BaiTianio/VLP/Data_Receive_analyze/Analyze_Python/2020_1_13实验分析/俯仰角/解决方法3/Picture/PDPD10-20.jpg

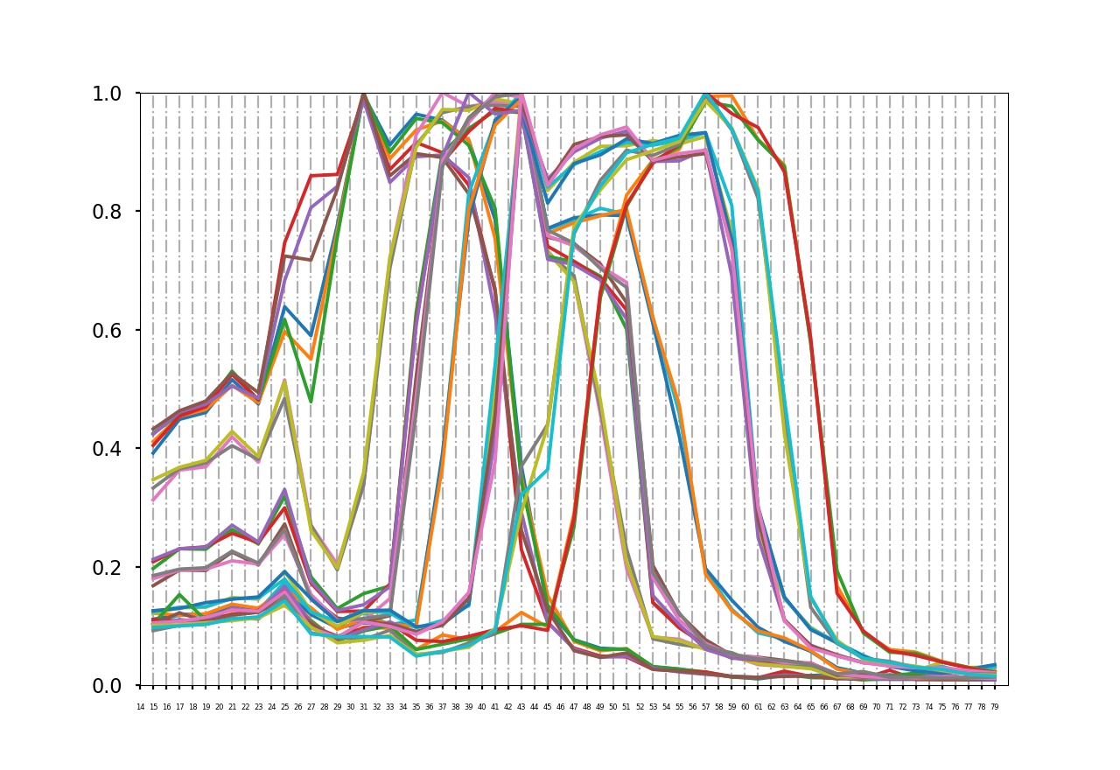
Data_Receive_analyze/Analyze_Python/2020_1_13实验分析/俯仰角/解决方法3/Picture/PDPD10-20.jpg
