BaiTianio/VLP/Data_Receive_analyze/Analyze_Matlab/picture/8PDsV2/PDarray1_39.jpg

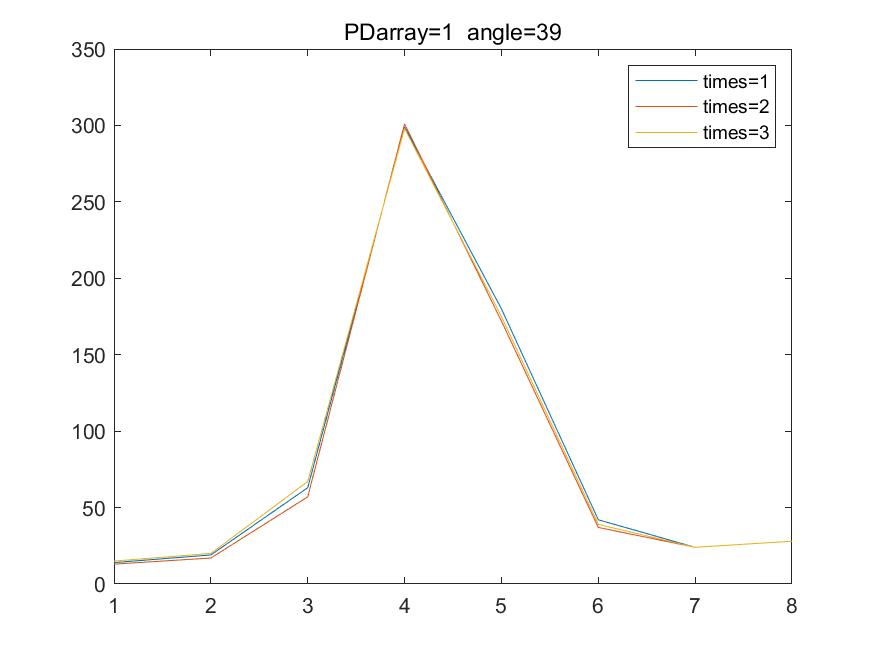
Data_Receive_analyze/Analyze_Matlab/picture/8PDsV2/PDarray1_39.jpg
