BaiTianio/VLP/Data_Receive_analyze/Analyze_Matlab/picture/8PDsV2/PDarray2_62.jpg

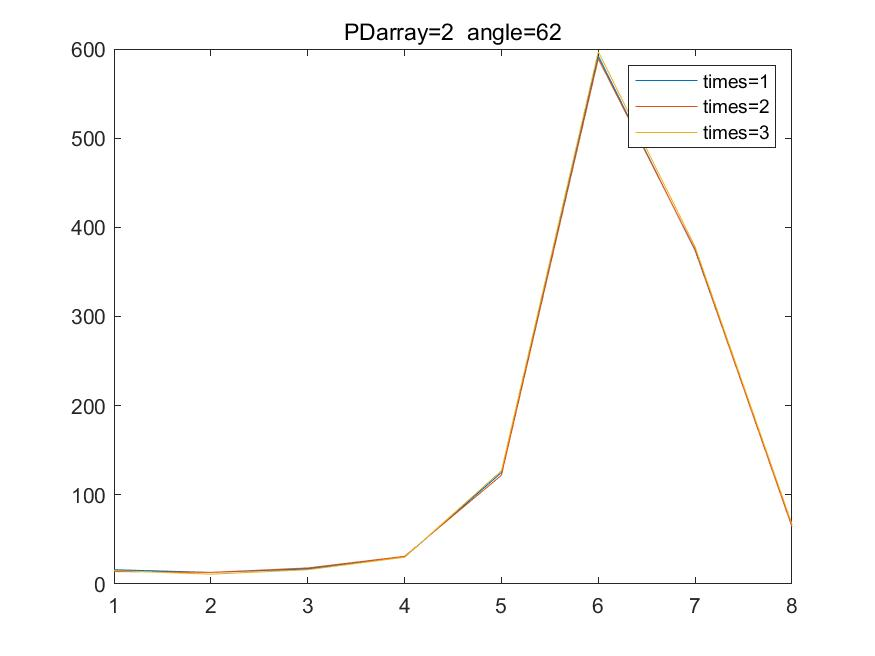
Data_Receive_analyze/Analyze_Matlab/picture/8PDsV2/PDarray2_62.jpg
