BaiTianio/VLP/Data_Receive_analyze/Analyze_Matlab/picture/8PDsV2/PDarray4_66.jpg

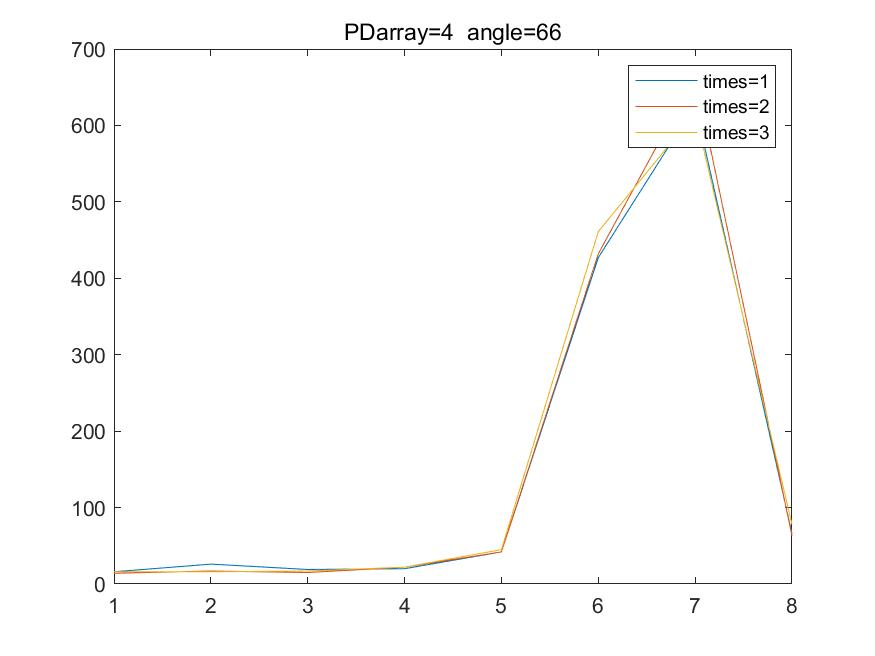
Data_Receive_analyze/Analyze_Matlab/picture/8PDsV2/PDarray4_66.jpg
