BaiTianio/VLP/Data_Receive_analyze/Analyze_Matlab/picture/32PDsV2/Angle_74.jpg

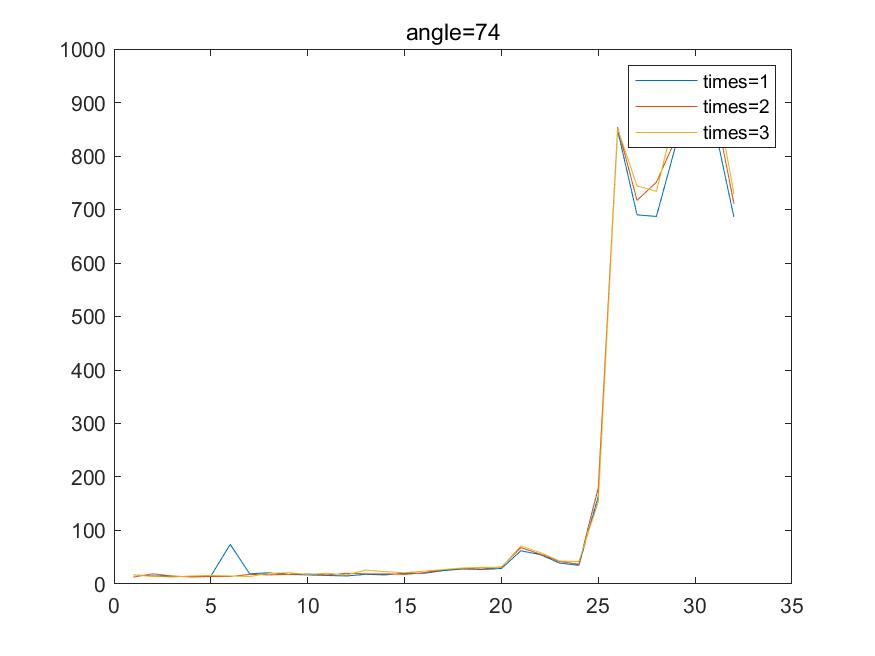
Data_Receive_analyze/Analyze_Matlab/picture/32PDsV2/Angle_74.jpg
