BaiTianio/VLP/Data_Receive_analyze/Analyze_Matlab/picture/32PDsV2/Angle_80.jpg

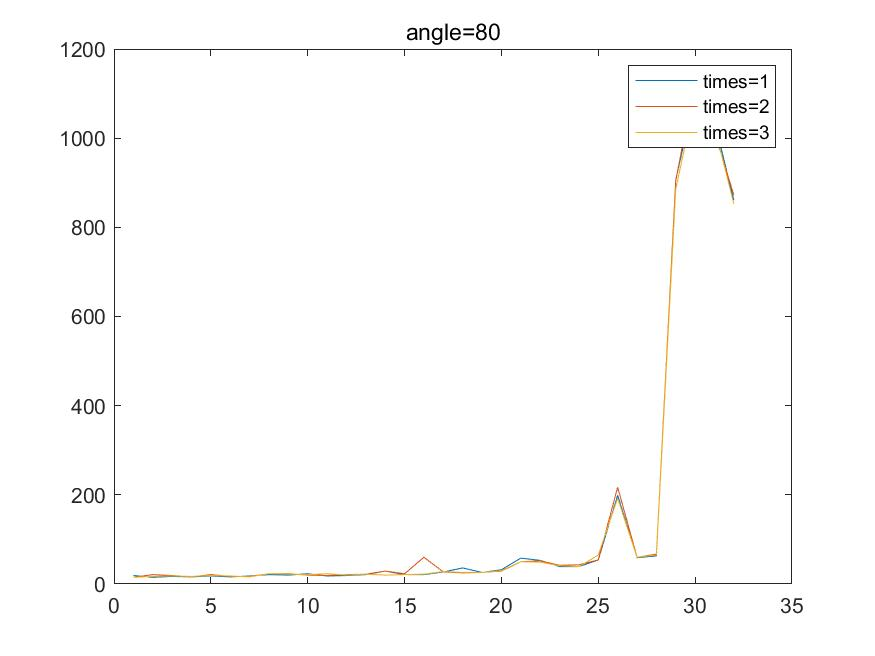
Data_Receive_analyze/Analyze_Matlab/picture/32PDsV2/Angle_80.jpg
