BaiTianio/VLP/Data_Receive_analyze/Analyze_Matlab/picture/SignlePD/PD32.jpg

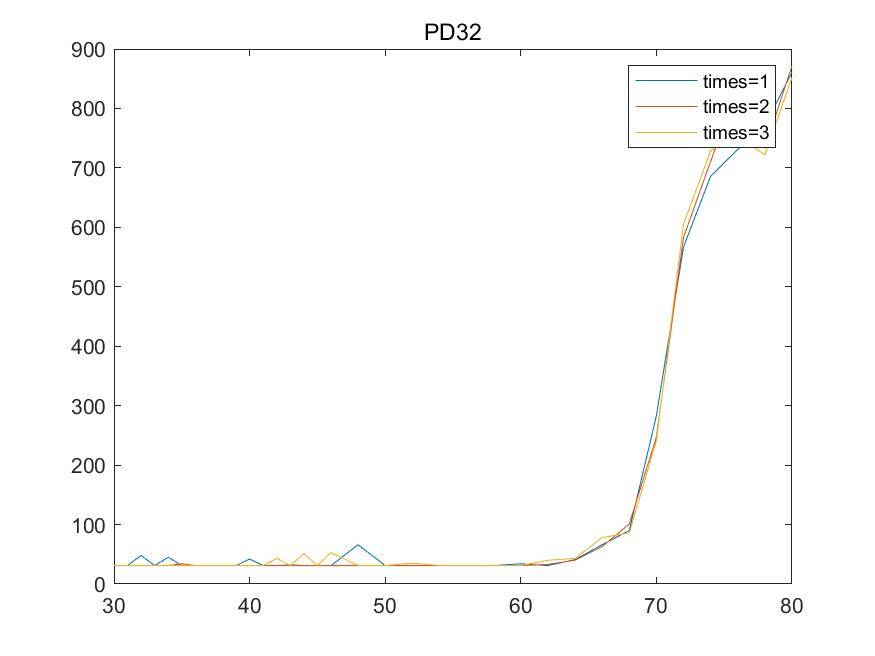
Data_Receive_analyze/Analyze_Matlab/picture/SignlePD/PD32.jpg
