BaiTianio/VLP/Data_Receive_analyze/Analyze_Python/2019_8_23实验分析/俯仰角/解决方法1/Picture/rearrange/31_1.jpg

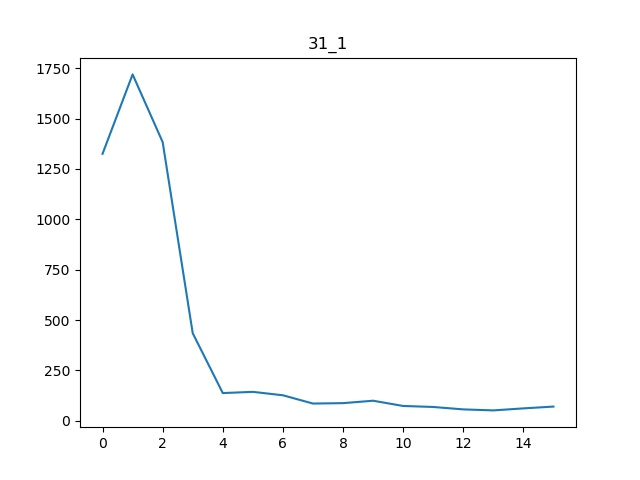
Data_Receive_analyze/Analyze_Python/2019_8_23实验分析/俯仰角/解决方法1/Picture/rearrange/31_1.jpg
