BaiTianio/VLP/Data_Receive_analyze/Analyze_Python/2019_8_23实验分析/水平角/picture/horizontalAngle_32PD/angle29_3.png

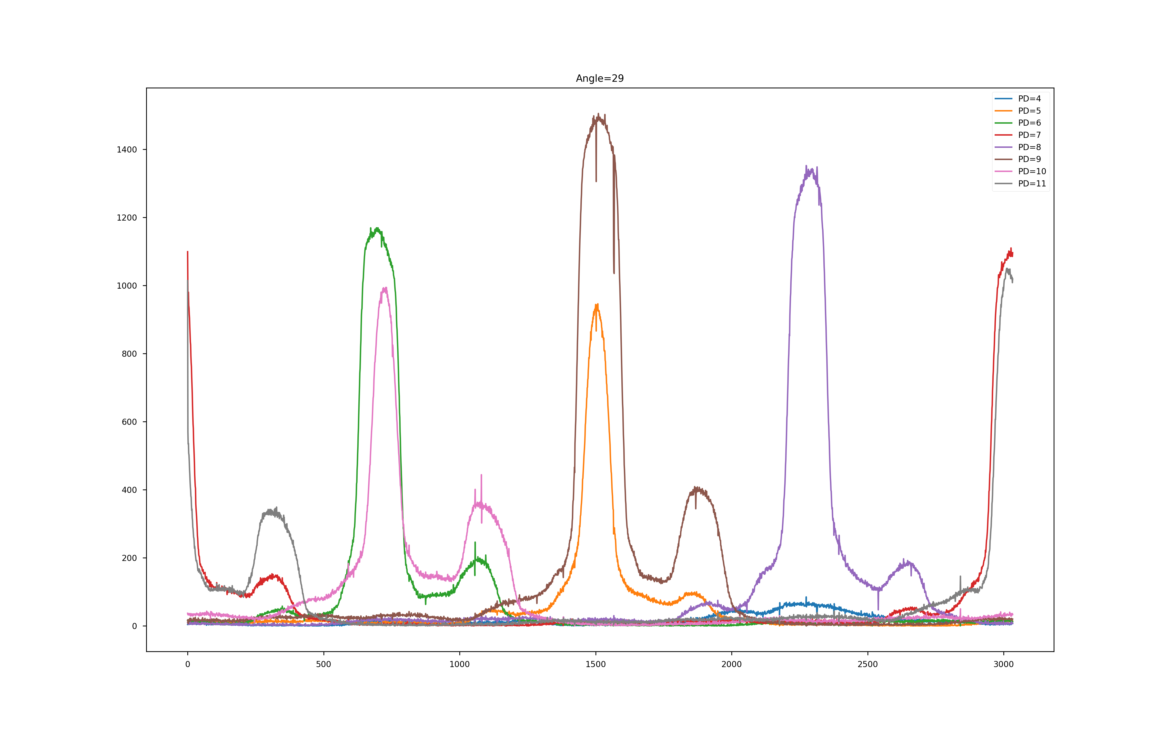
Data_Receive_analyze/Analyze_Python/2019_8_23实验分析/水平角/picture/horizontalAngle_32PD/angle29_3.png
