BaiTianio/VLP/Data_Receive_analyze/Analyze_Python/2020_1_13实验分析/俯仰角/解决方法1/Picture/singlePD/PD20.jpg

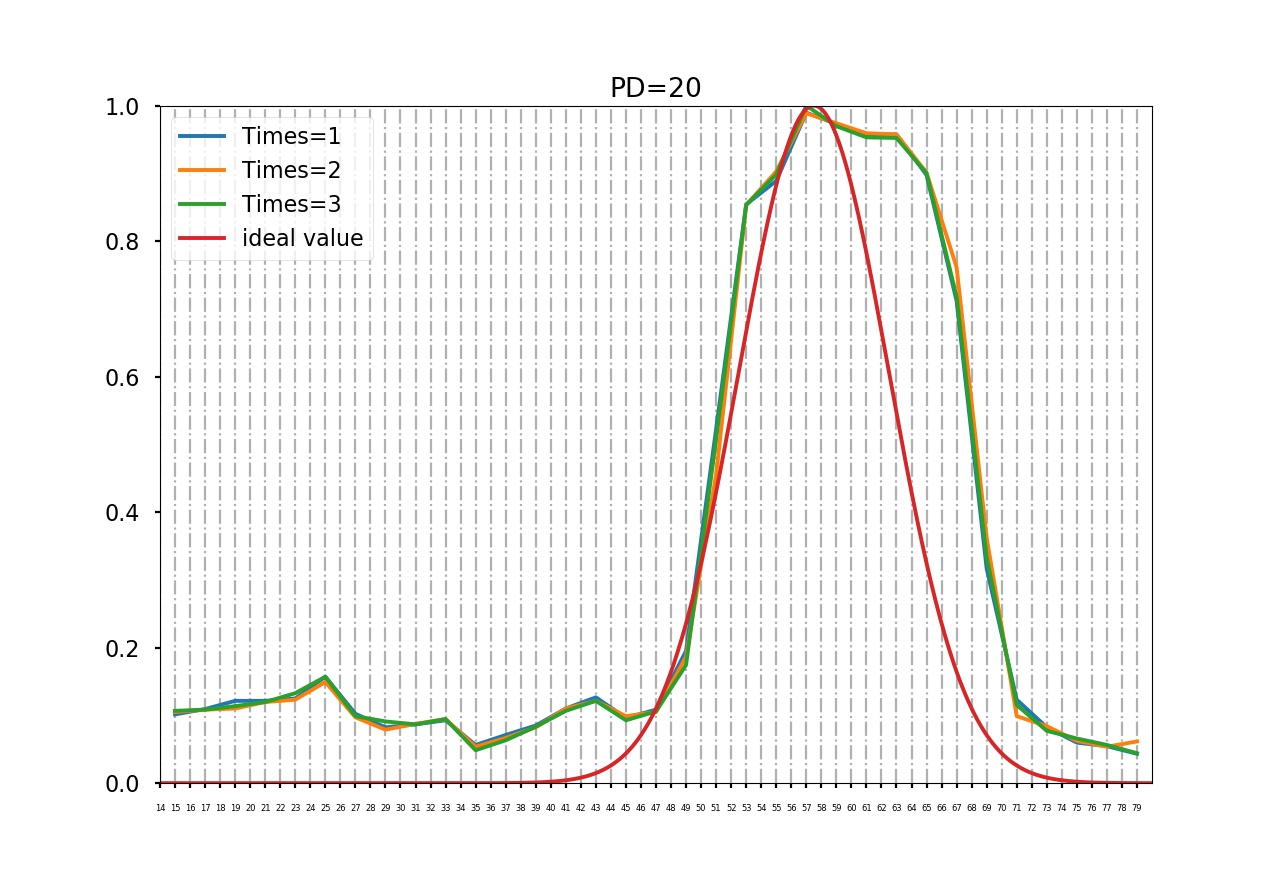
Data_Receive_analyze/Analyze_Python/2020_1_13实验分析/俯仰角/解决方法1/Picture/singlePD/PD20.jpg
