BaiTianio/VLP/Data_Receive_analyze/DataStroge/2019_8_23/Picture/siglePD_15_79/20.jpg

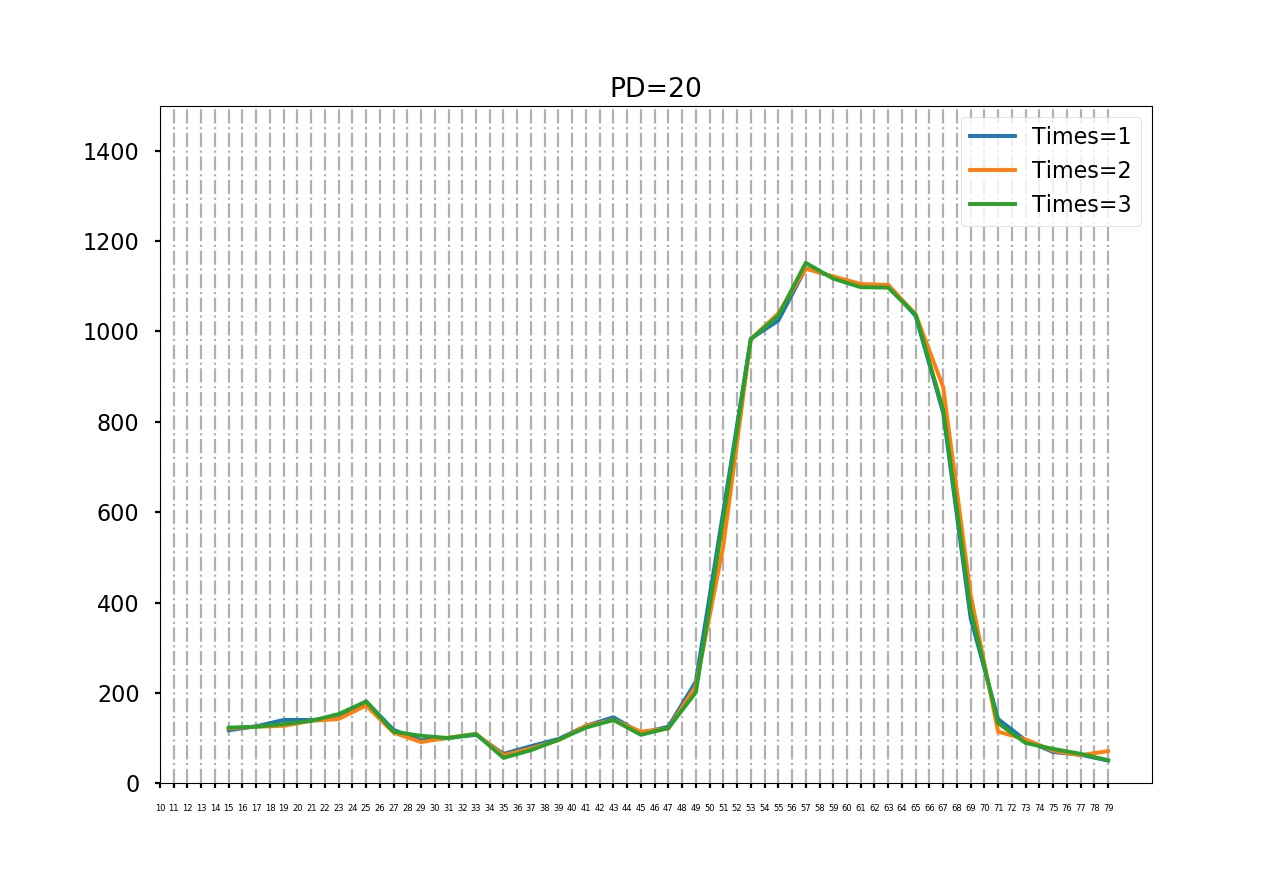
Data_Receive_analyze/DataStroge/2019_8_23/Picture/siglePD_15_79/20.jpg
