BaiTianio/VLP/Receiver/Construction_Design(SW)/转台/V3/电机.SLDPRT

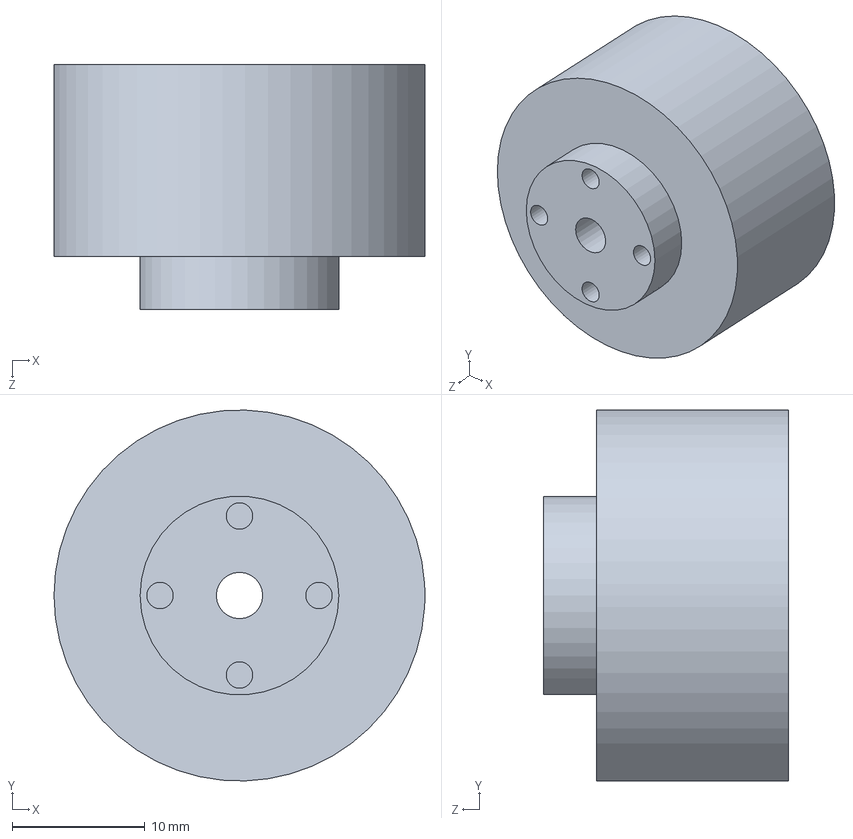
[picture p196: CAD file, 2020-01-13]
Receiver/Construction_Design(SW)/转台/V3/电机.SLDPRT
28.0 x 28.0 x 18.5 mm
