BaiTianio/VLP/Receiver/Construction_Design(SW)/转台/V3/齿轮/3号齿轮Part_a.SLDPRT

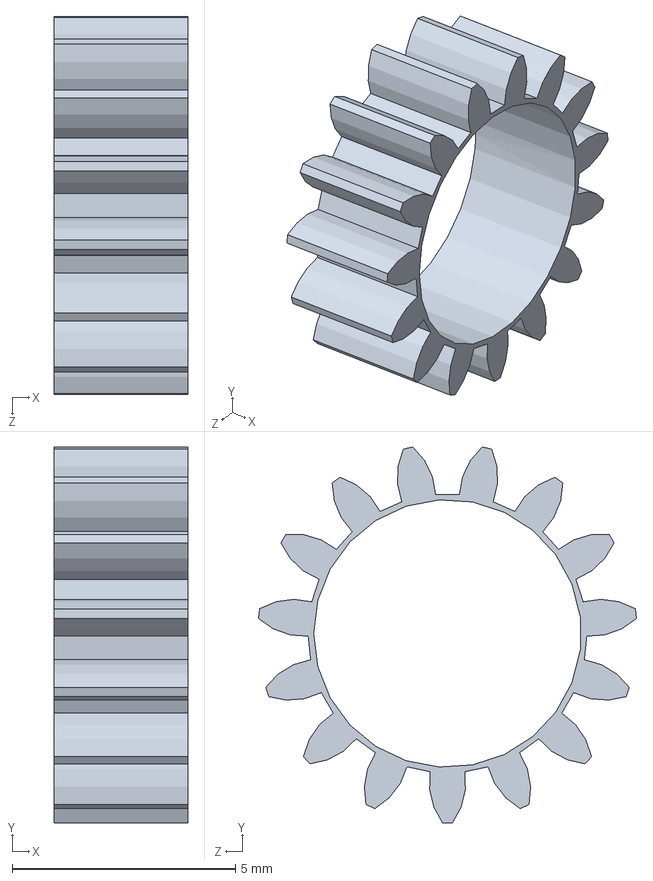
[picture p197: CAD file, 2020-01-13]
Receiver/Construction_Design(SW)/转台/V3/齿轮/3号齿轮Part_a.SLDPRT
3.00 x 8.43 x 8.47 mm
