BaiTianio/VLP/Receiver/Construction_Design(SW)/转台/V3/齿轮/2号齿轮Part_c.SLDPRT

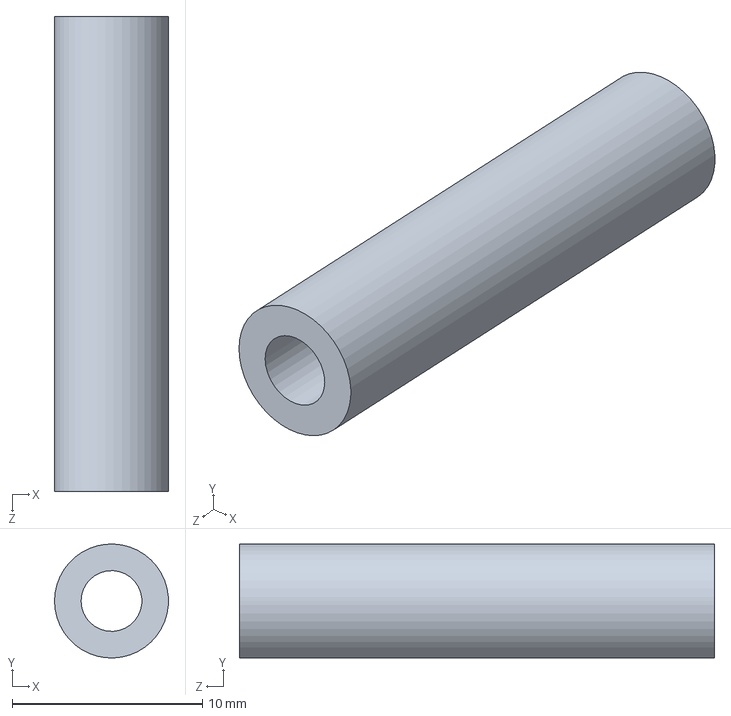
[picture p198: CAD file, 2020-01-13]
Receiver/Construction_Design(SW)/转台/V3/齿轮/2号齿轮Part_c.SLDPRT
6.00 x 6.00 x 25.0 mm
