BaiTianio/VLP/Receiver/Construction_Design(SW)/转台/V3/齿轮/3号齿轮Part_c.SLDPRT

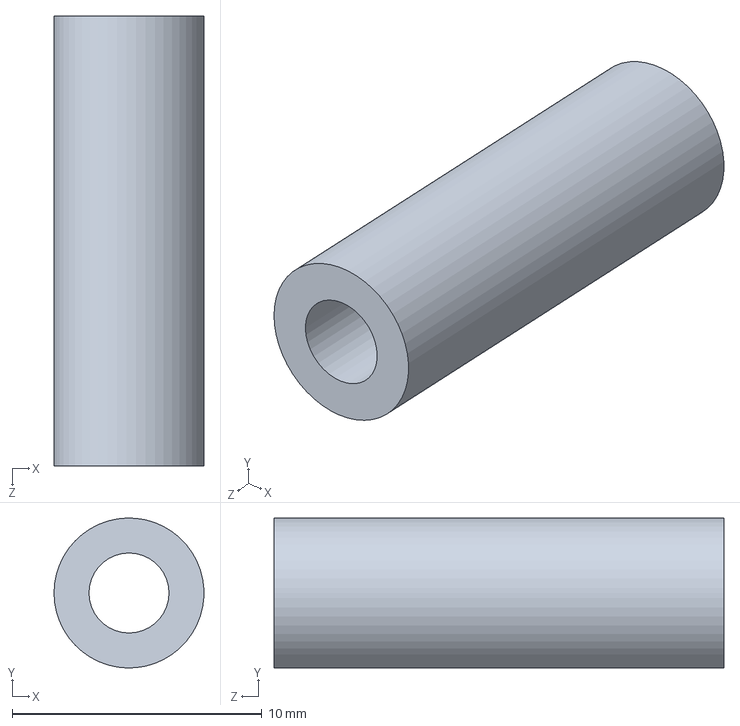
[picture p199: CAD file, 2020-01-13]
Receiver/Construction_Design(SW)/转台/V3/齿轮/3号齿轮Part_c.SLDPRT
6.00 x 6.00 x 18.0 mm
