BaiTianio/VLP/Receiver/Construction_Design(SW)/转台/V3/齿轮/4号齿轮Part_b.SLDPRT

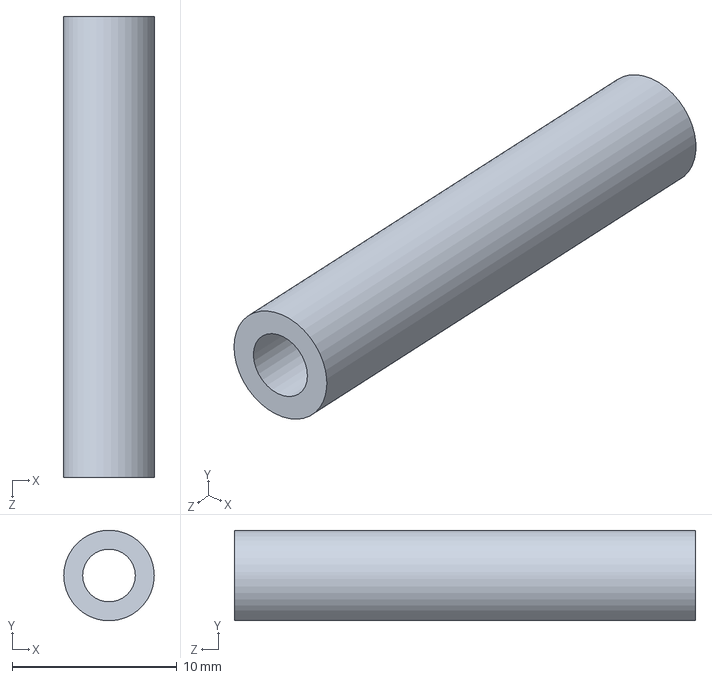
[picture p200: CAD file, 2020-01-13]
Receiver/Construction_Design(SW)/转台/V3/齿轮/4号齿轮Part_b.SLDPRT
5.50 x 5.50 x 28.0 mm
