BaiTianio/VLP/Receiver/Construction_Design(SW)/V2/传感器部分/16PD.JPG

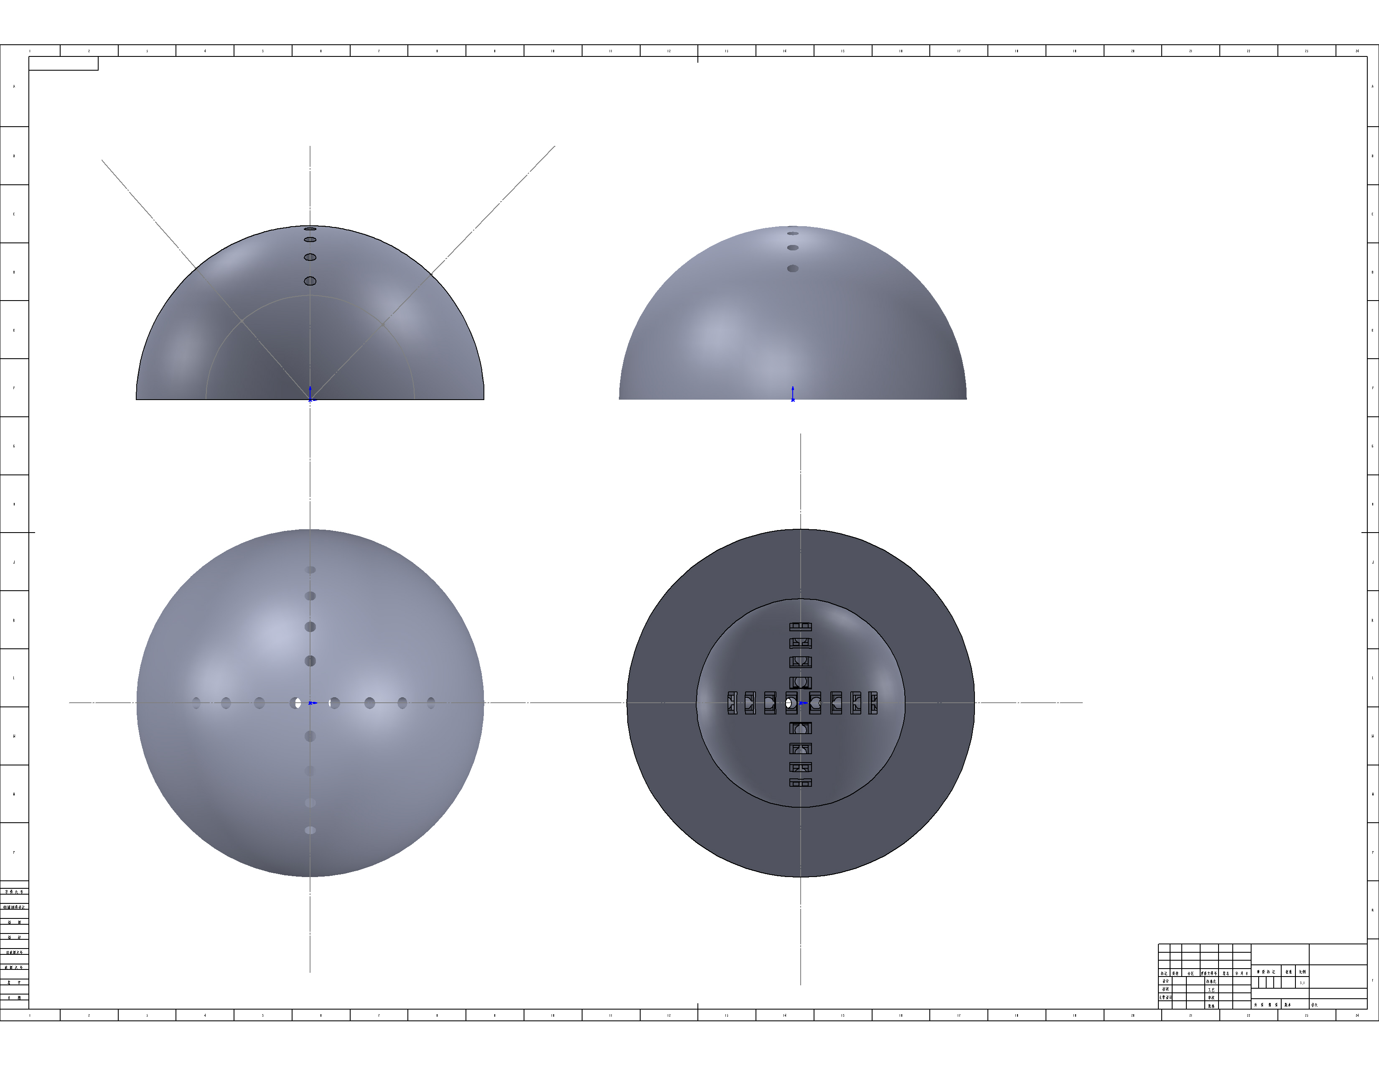
Receiver/Construction_Design(SW)/V2/传感器部分/16PD.JPG
