BaiTianio/VLP/Receiver/Construction_Design(SW)/转台/V3/底座.JPG

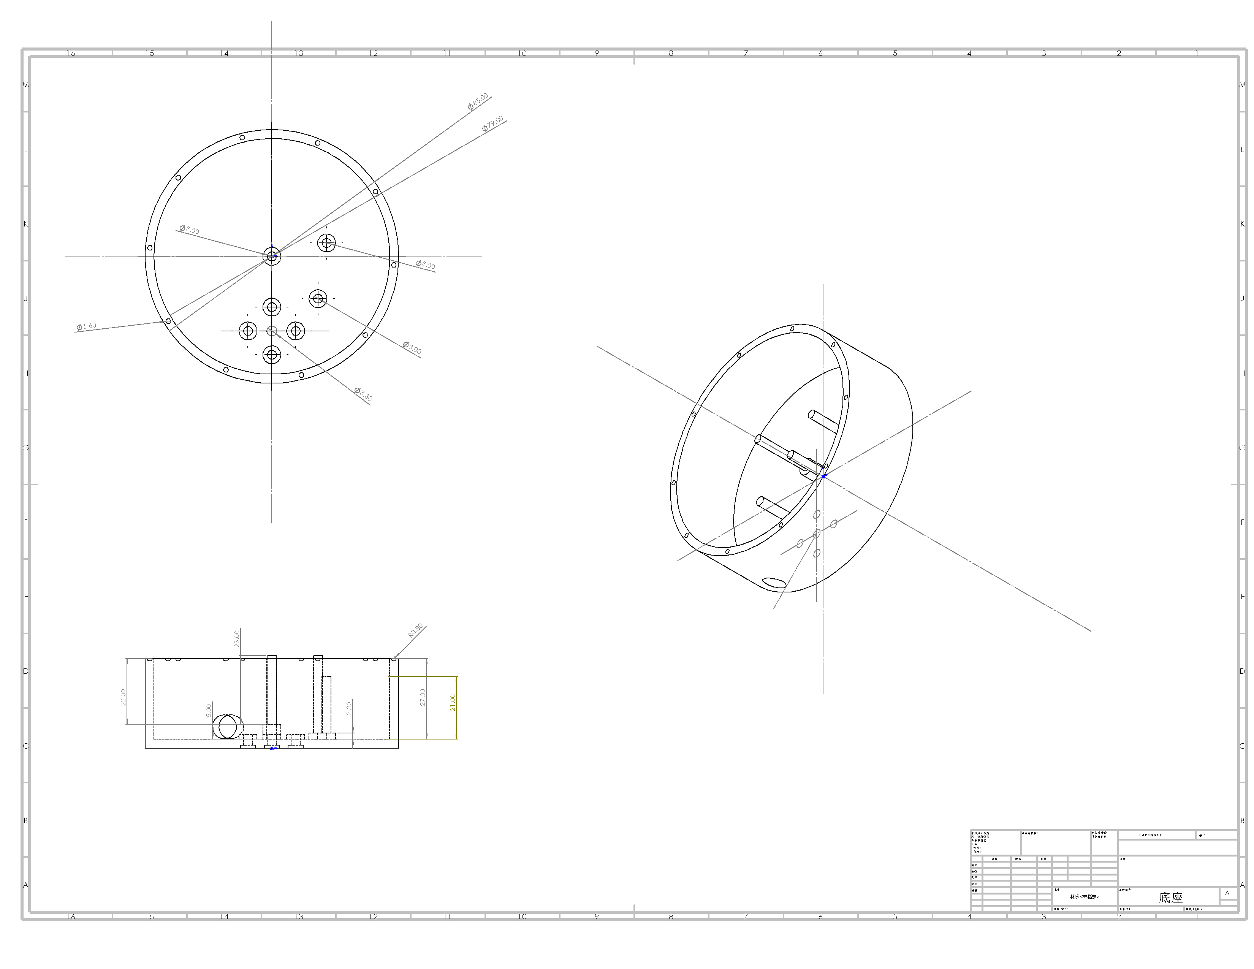
Receiver/Construction_Design(SW)/转台/V3/底座.JPG
